AI6YP/meduza/eagle/meduza01/images/P1040016.JPG

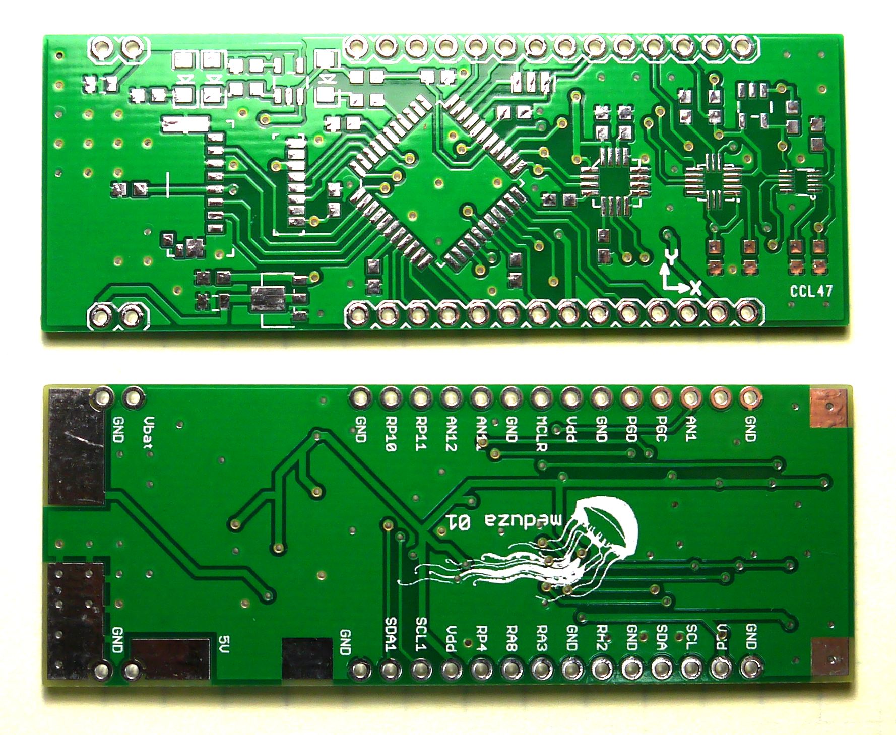
eagle/meduza01/images/P1040016.JPG
